ivanseidel/Primo/Photos-Bricks/Bricks.jpg

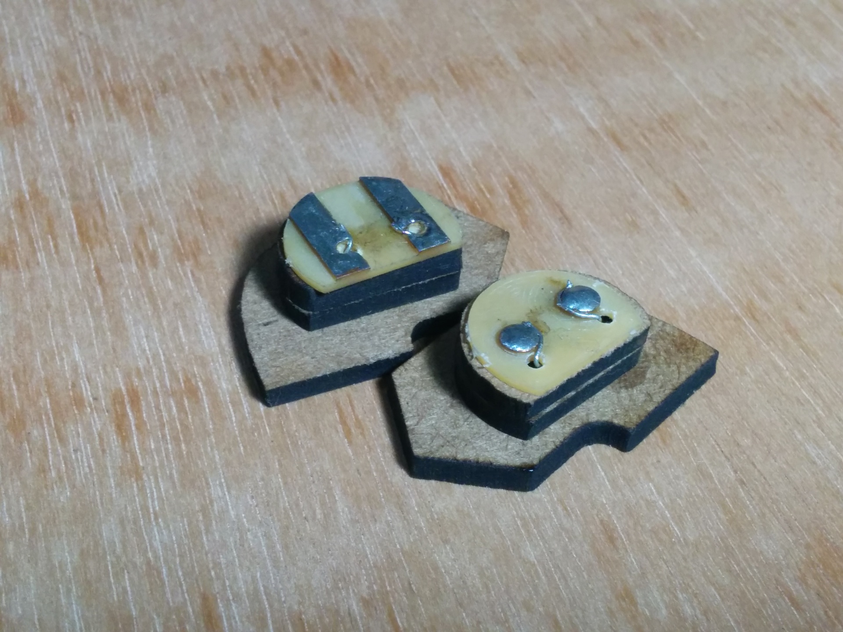
Photos-Bricks/Bricks.jpg
