ivanseidel/Primo/Photos-Cubetto/Cubetto_02.jpg

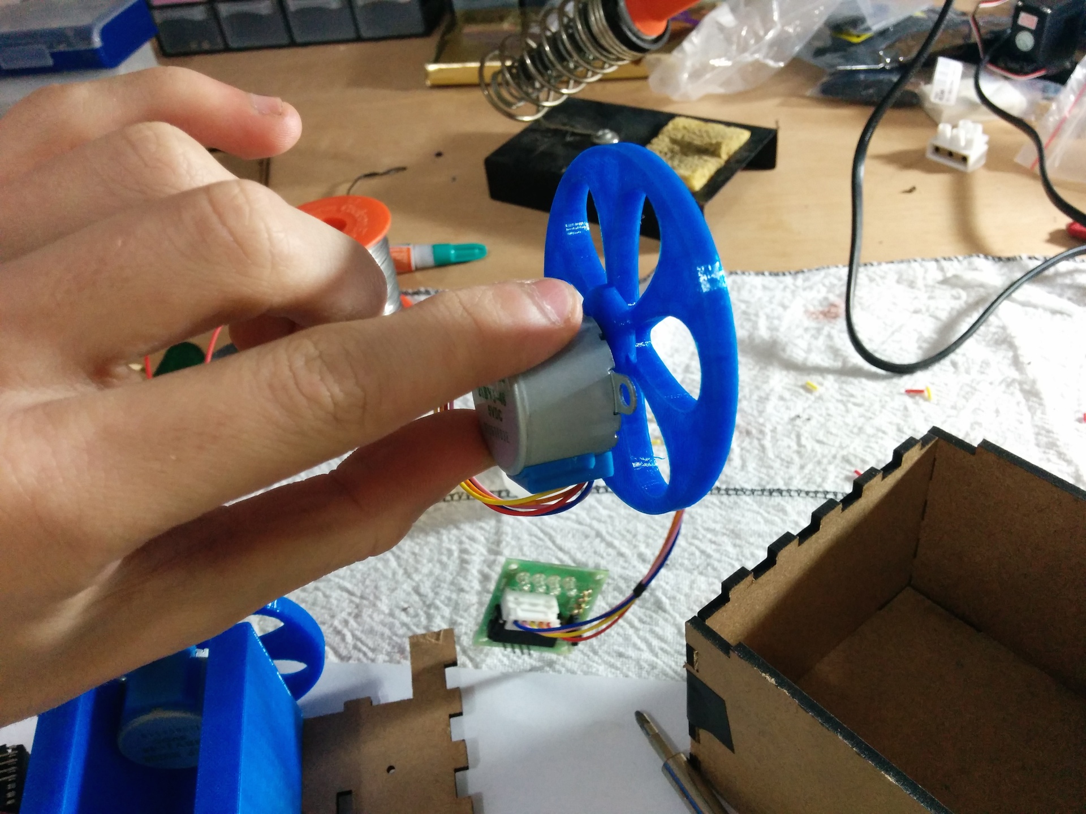
Photos-Cubetto/Cubetto_02.jpg
