ivanseidel/Primo/Photos-Cubetto/Cubetto_03.jpg

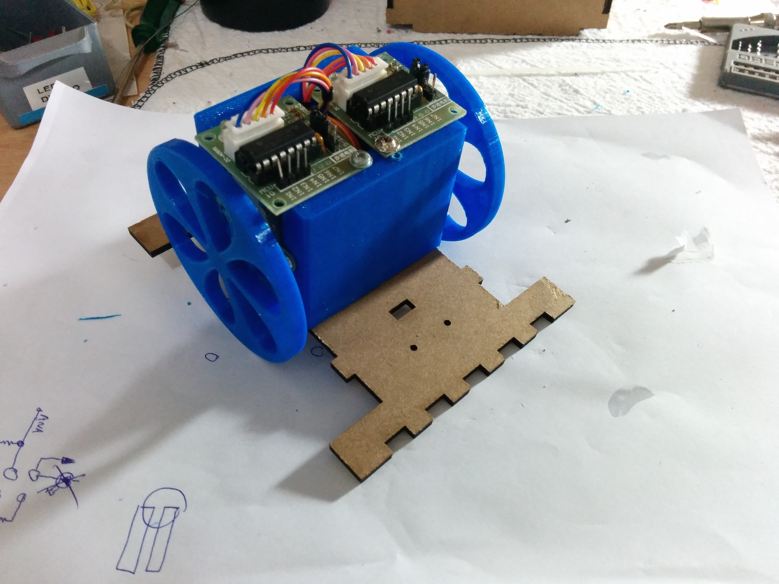
Photos-Cubetto/Cubetto_03.jpg
