ivanseidel/Primo/Photos-Cubetto/Cubetto_04.jpg

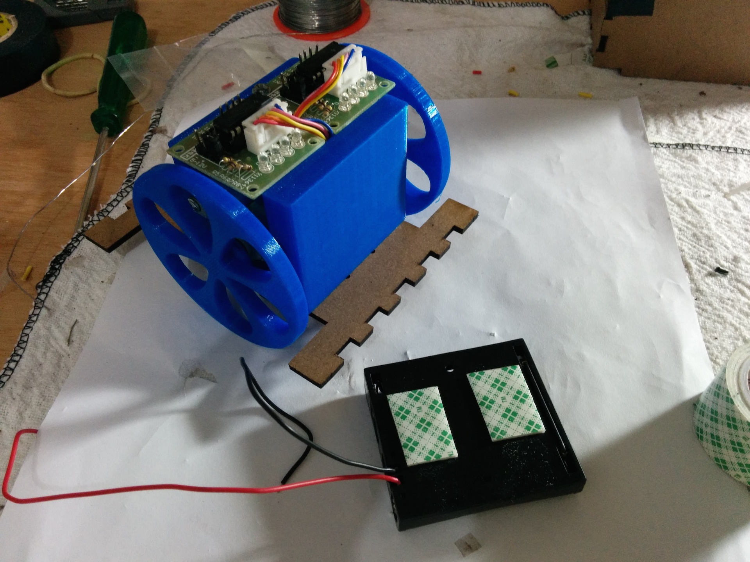
Photos-Cubetto/Cubetto_04.jpg
