ivanseidel/Primo/Photos-Cubetto/Cubetto_05.jpg

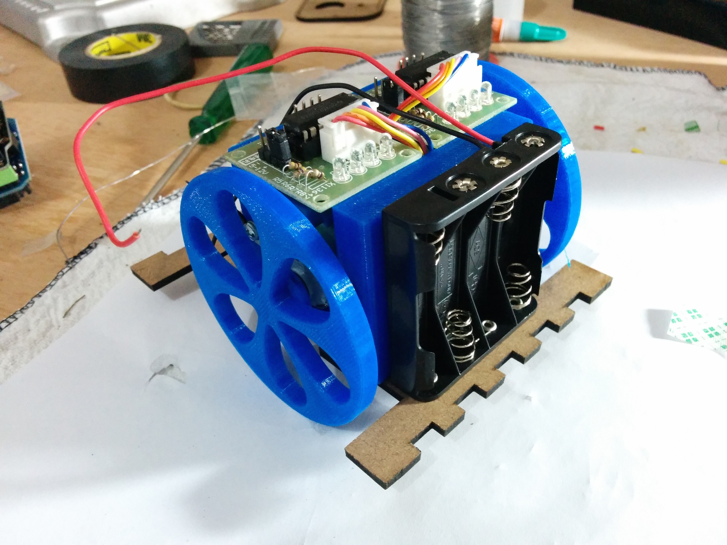
Photos-Cubetto/Cubetto_05.jpg
