ivanseidel/Primo/Photos-Cubetto/Cubetto_06.jpg

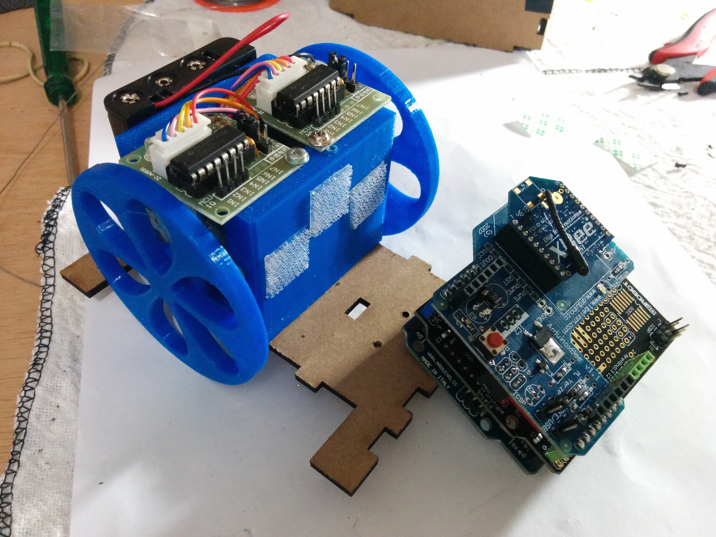
Photos-Cubetto/Cubetto_06.jpg
