ivanseidel/Primo/Photos-Cubetto/Cubetto_07.jpg

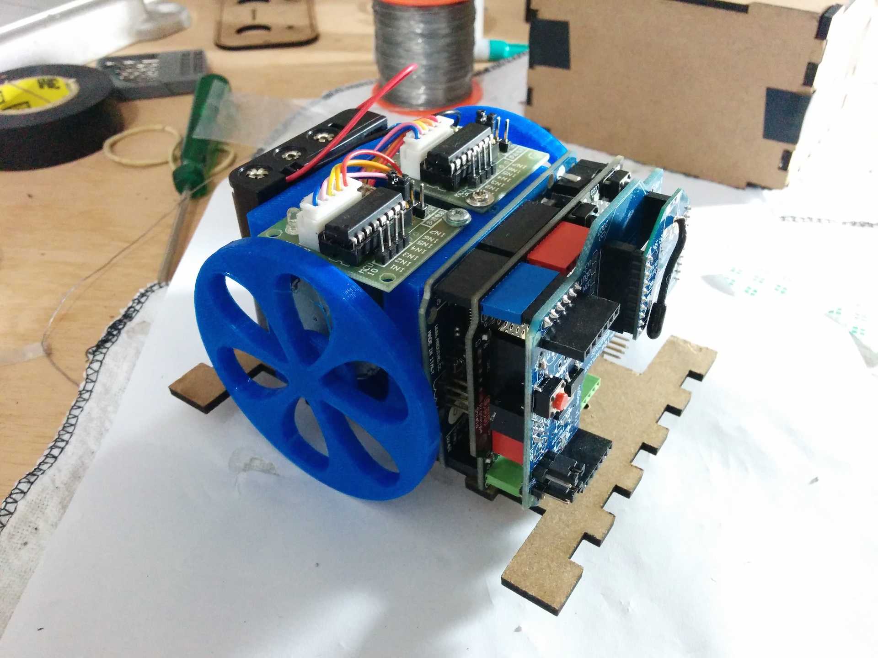
Photos-Cubetto/Cubetto_07.jpg
