ivanseidel/Primo/Photos-Cubetto/Cubetto_08.jpg

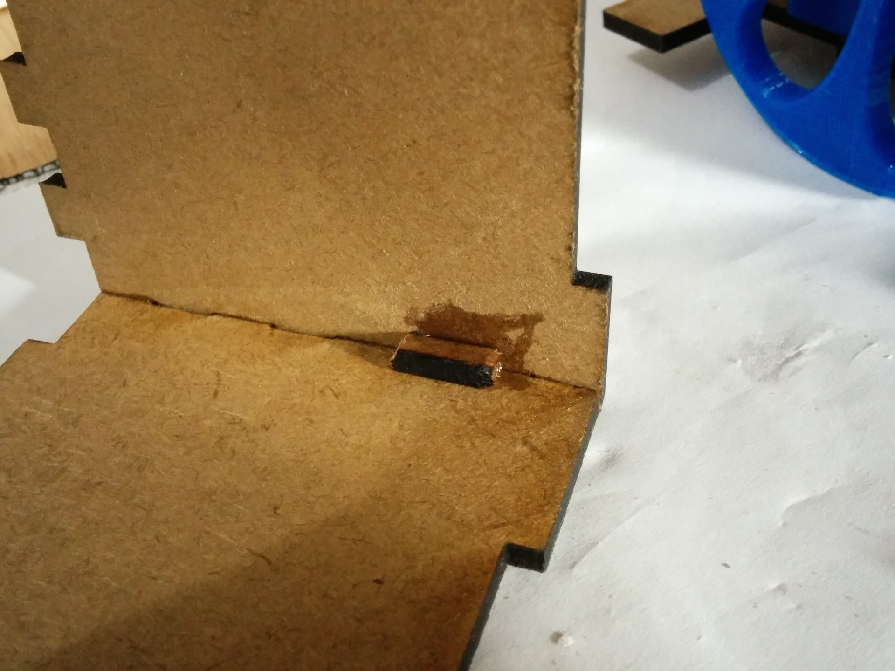
Photos-Cubetto/Cubetto_08.jpg
