ivanseidel/Primo/Photos-Cubetto/Cubetto_09.jpg

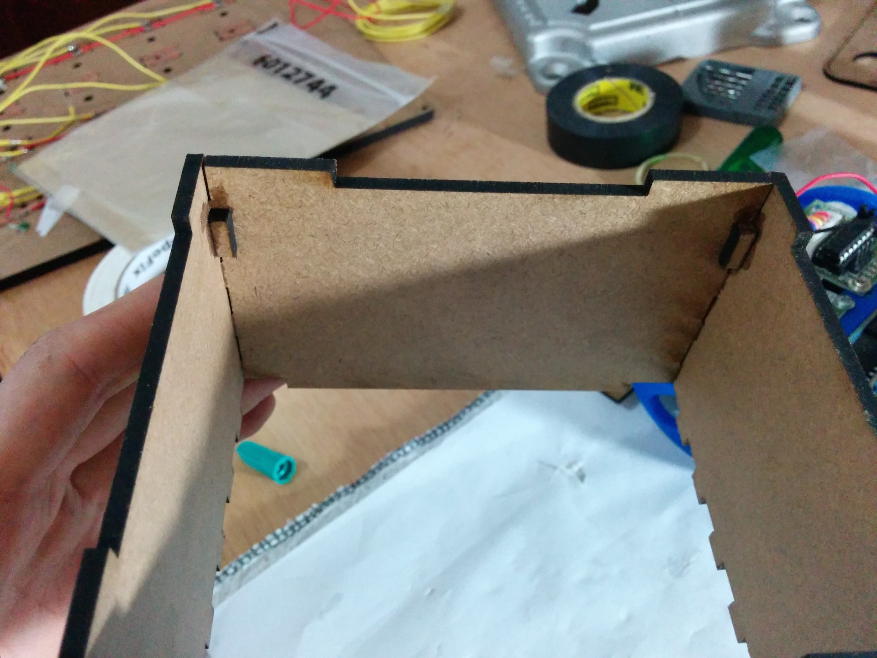
Photos-Cubetto/Cubetto_09.jpg
