ivanseidel/Primo/Photos-Cubetto/Cubetto_10.jpg

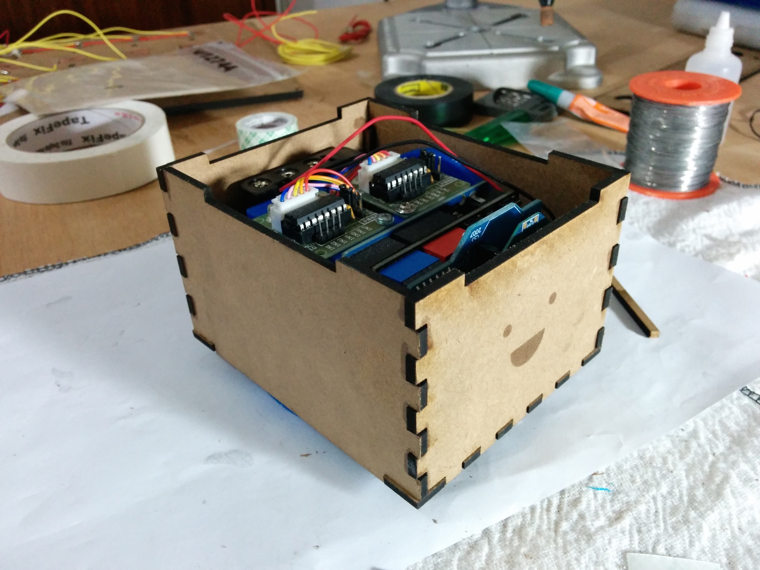
Photos-Cubetto/Cubetto_10.jpg
