ivanseidel/Primo/Photos-Cubetto/Cubetto_11.jpg

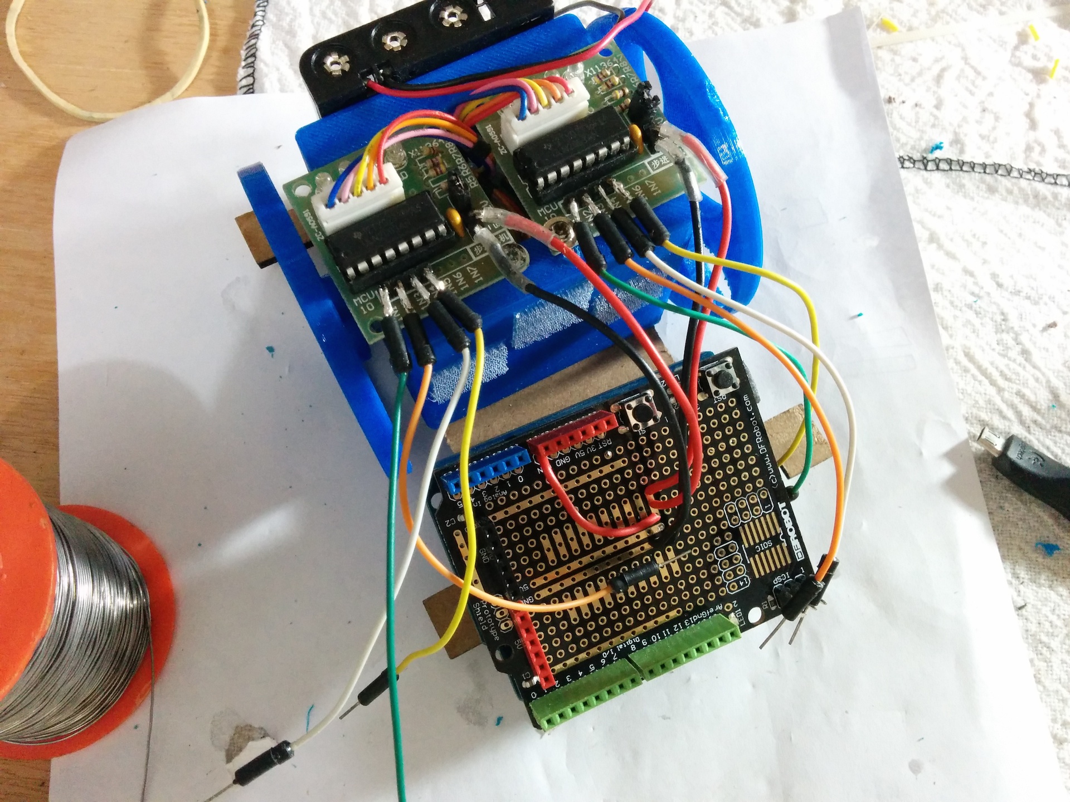
Photos-Cubetto/Cubetto_11.jpg
