ivanseidel/Primo/Photos-MainBoard/MainBoard_01.jpg

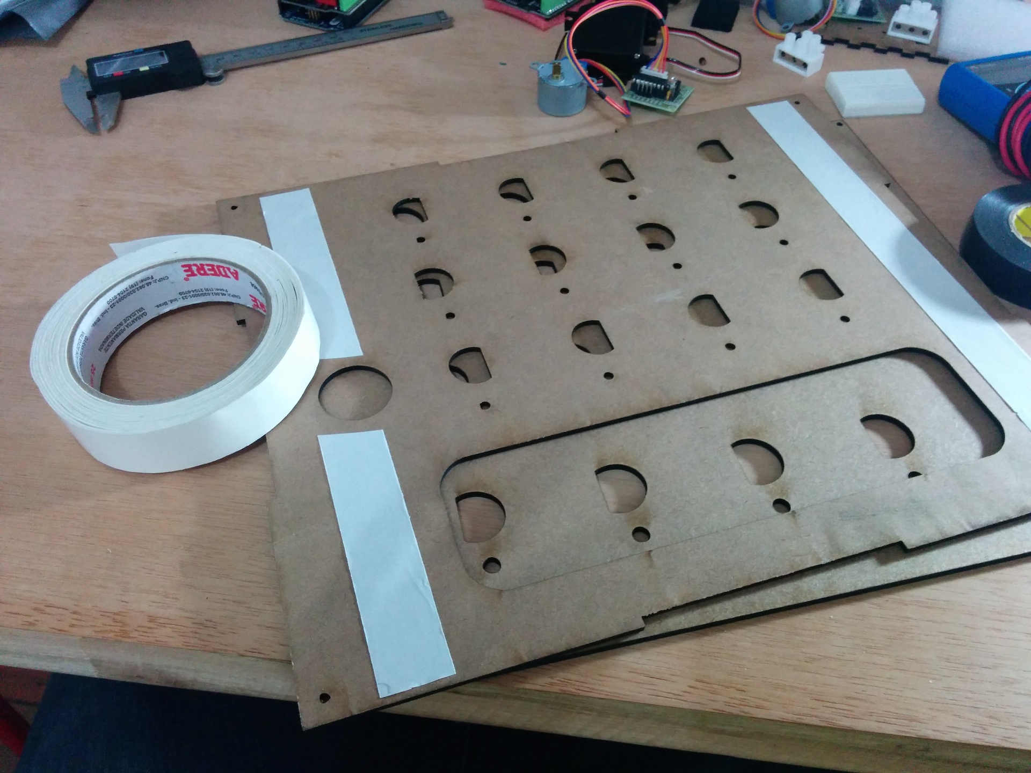
Photos-MainBoard/MainBoard_01.jpg
