ivanseidel/Primo/Photos-MainBoard/MainBoard_02.jpg

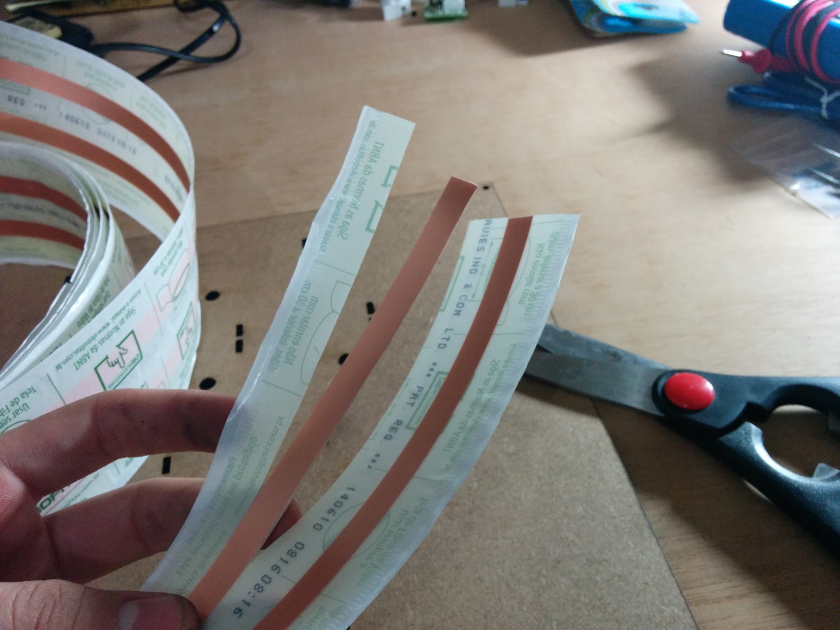
Photos-MainBoard/MainBoard_02.jpg
