ivanseidel/Primo/Photos-MainBoard/MainBoard_03.jpg

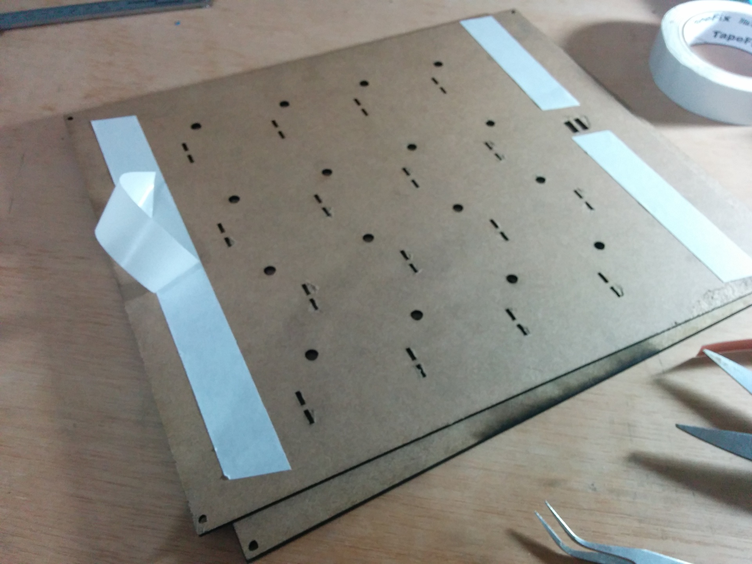
Photos-MainBoard/MainBoard_03.jpg
