ivanseidel/Primo/Photos-MainBoard/MainBoard_05.jpg

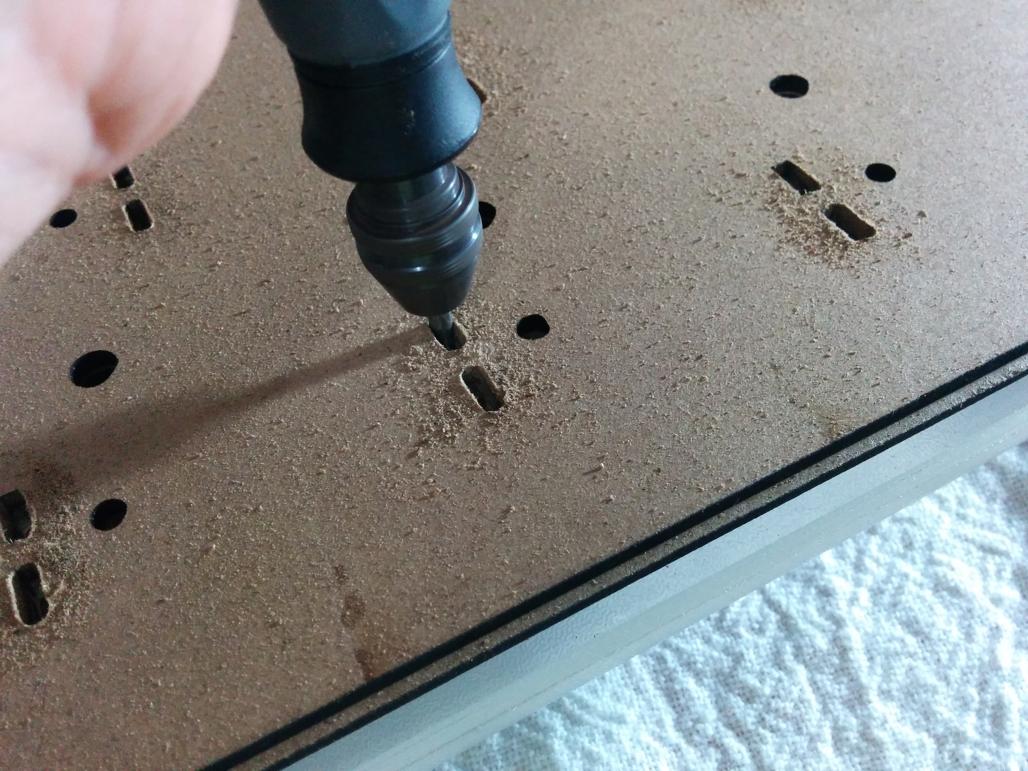
Photos-MainBoard/MainBoard_05.jpg
