ivanseidel/Primo/Photos-MainBoard/MainBoard_06.jpg

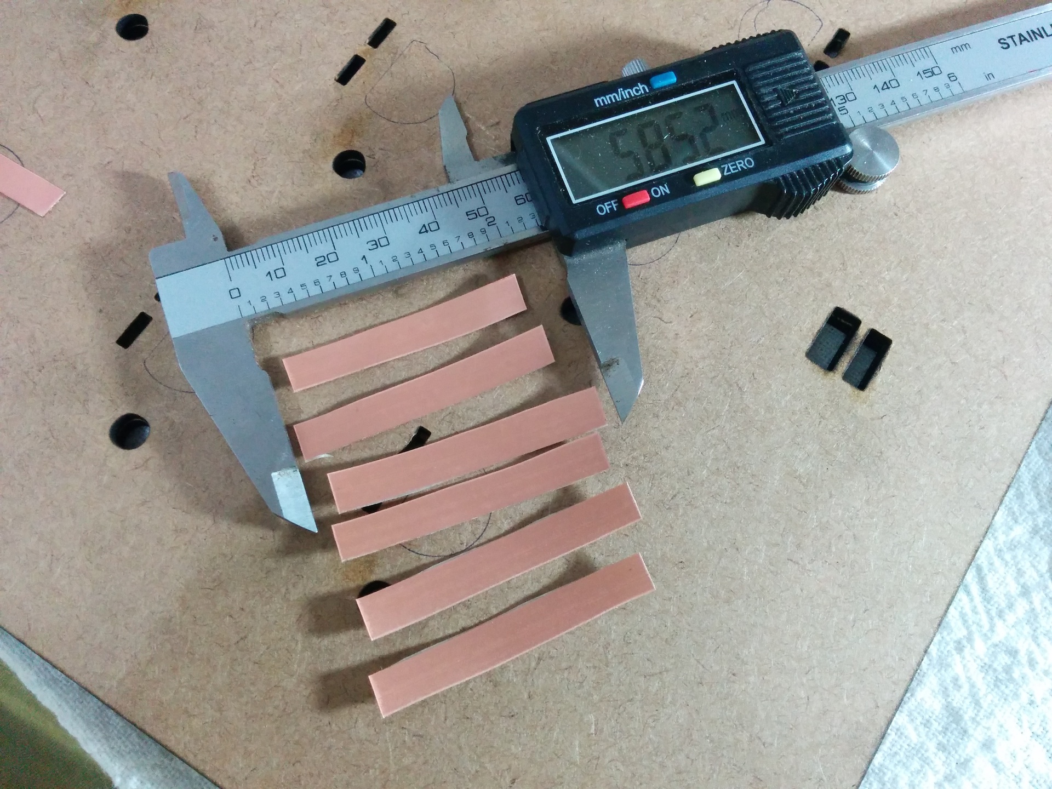
Photos-MainBoard/MainBoard_06.jpg
