ivanseidel/Primo/Photos-MainBoard/MainBoard_08.jpg

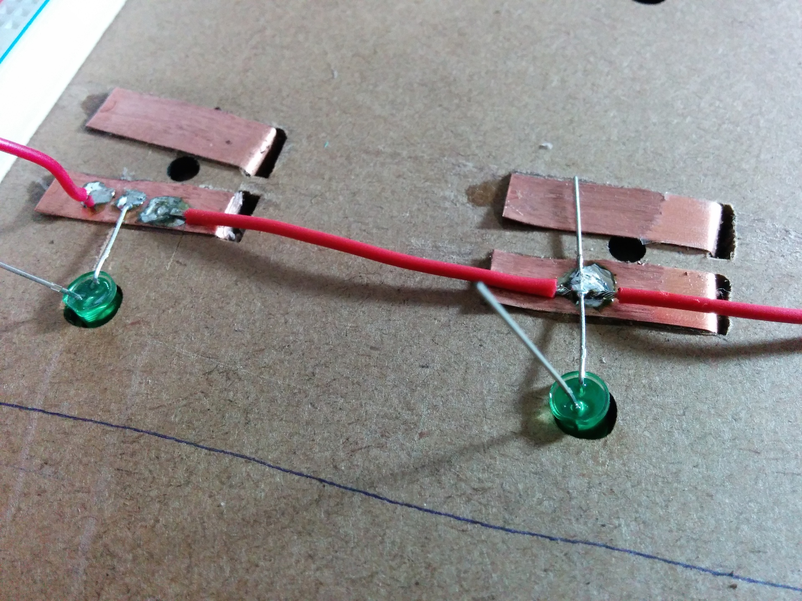
Photos-MainBoard/MainBoard_08.jpg
