ivanseidel/Primo/Photos-MainBoard/MainBoard_09.jpg

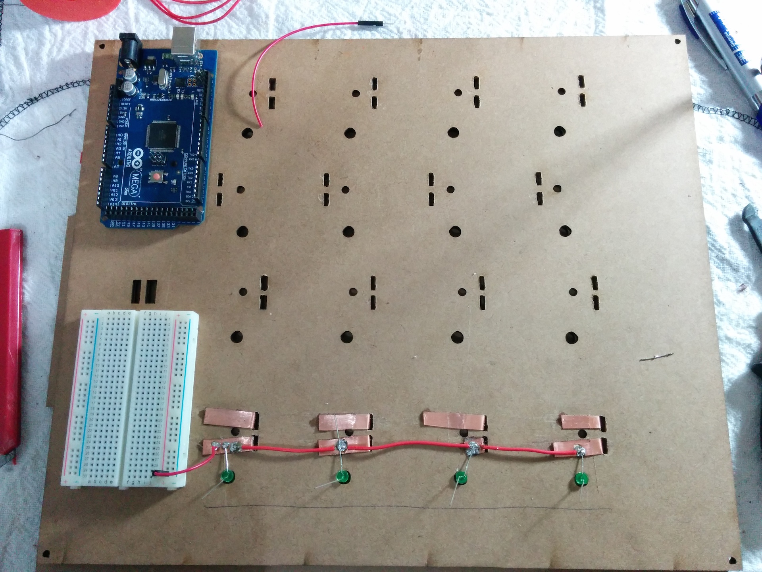
Photos-MainBoard/MainBoard_09.jpg
