ivanseidel/Primo/Photos-MainBoard/MainBoard_11.jpg

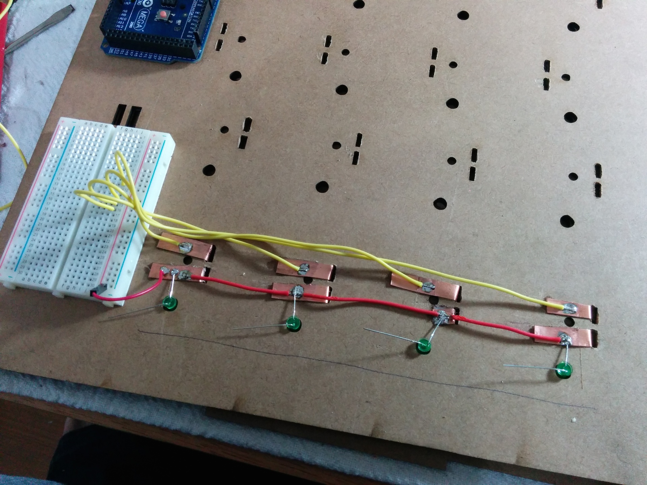
Photos-MainBoard/MainBoard_11.jpg
