ivanseidel/Primo/Photos-MainBoard/MainBoard_12.jpg

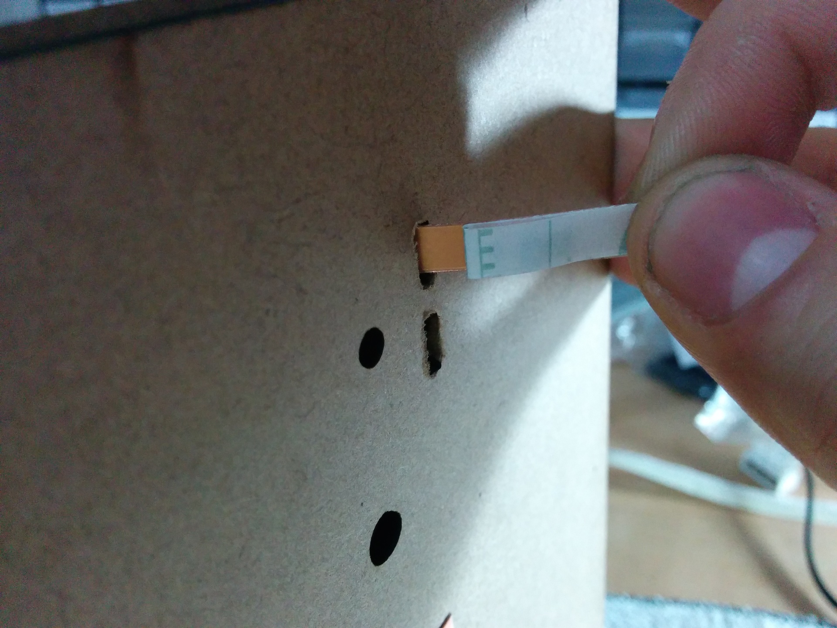
Photos-MainBoard/MainBoard_12.jpg
