ivanseidel/Primo/Photos-MainBoard/MainBoard_13.jpg

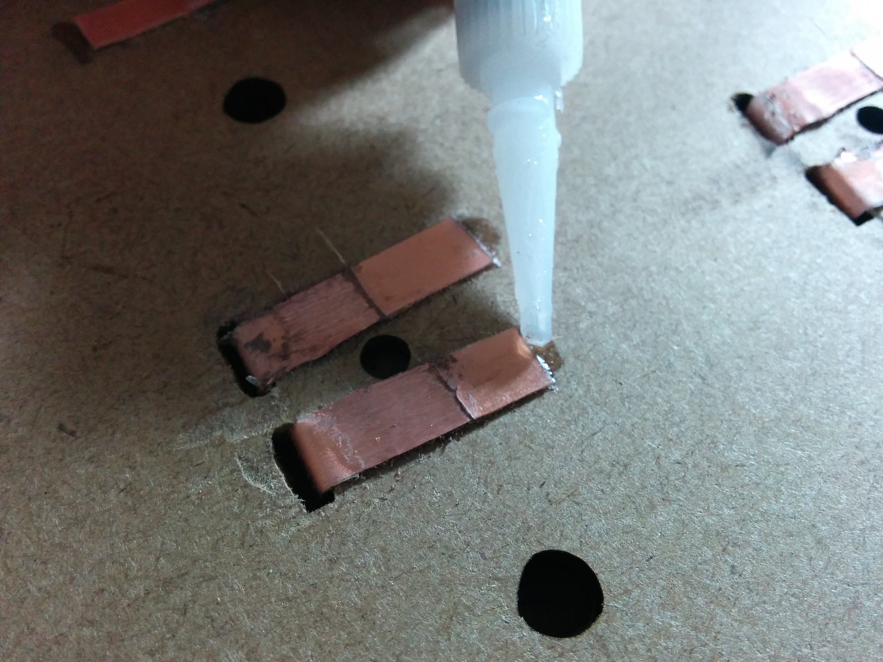
Photos-MainBoard/MainBoard_13.jpg
