ivanseidel/Primo/Photos-MainBoard/MainBoard_14.jpg

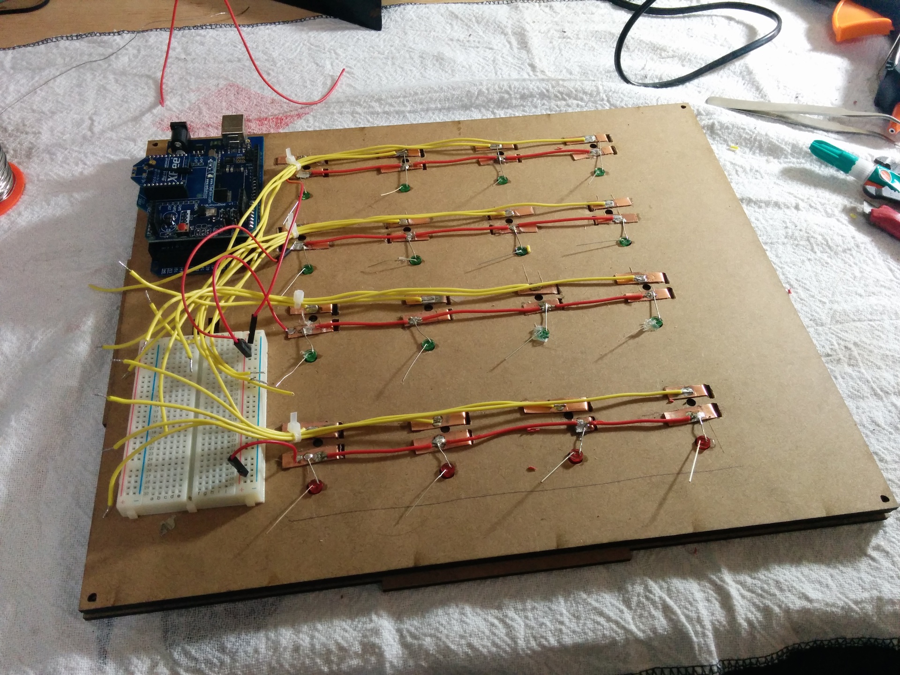
Photos-MainBoard/MainBoard_14.jpg
