ivanseidel/Primo/Photos-MainBoard/MainBoard_15.jpg

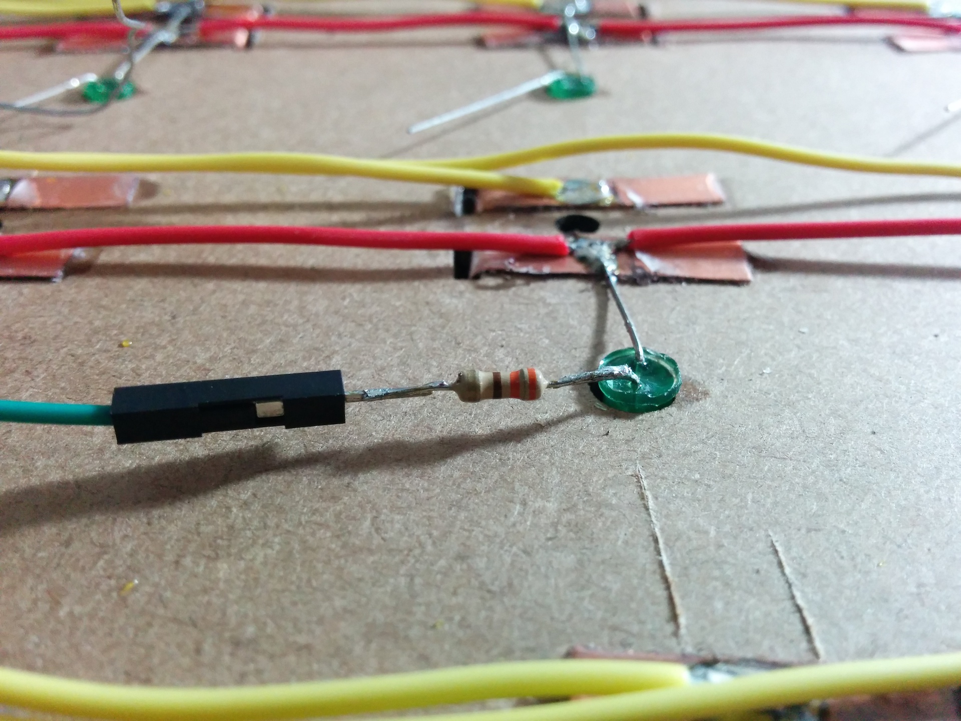
Photos-MainBoard/MainBoard_15.jpg
