ivanseidel/Primo/Photos-MainBoard/MainBoard_16.jpg

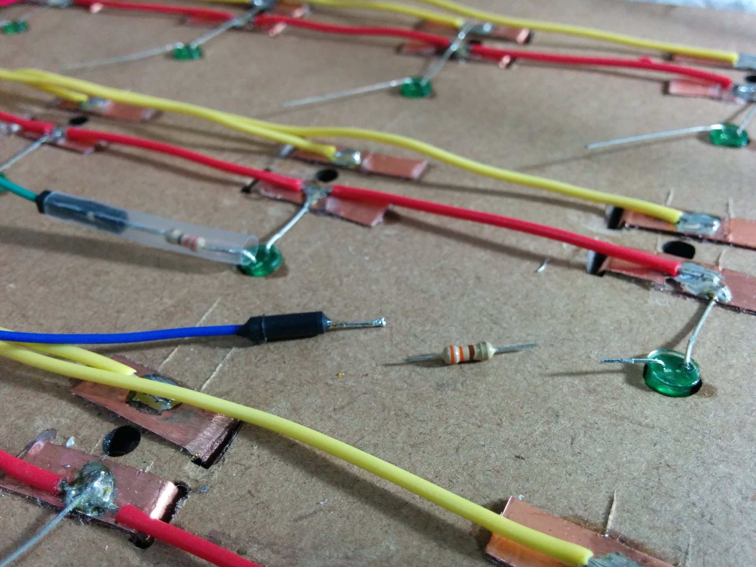
Photos-MainBoard/MainBoard_16.jpg
