ivanseidel/Primo/Photos-MainBoard/MainBoard_17.jpg

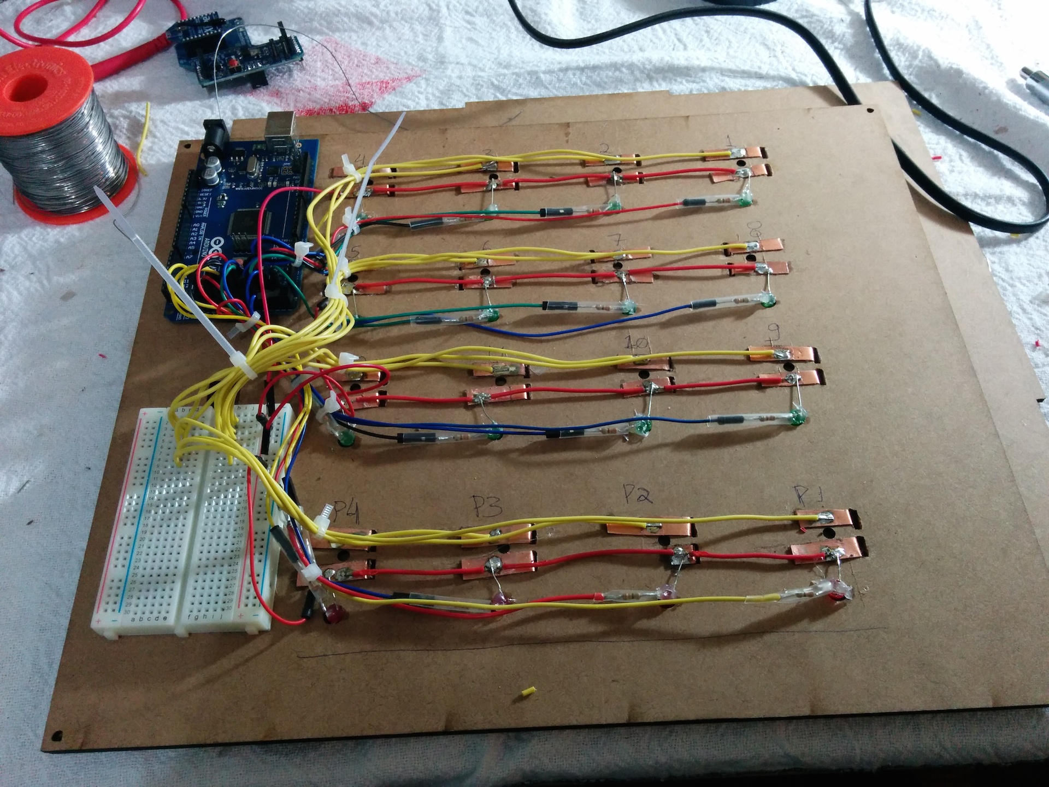
Photos-MainBoard/MainBoard_17.jpg
