ivanseidel/Primo/Photos-MainBoard/MainBoard_18.jpg

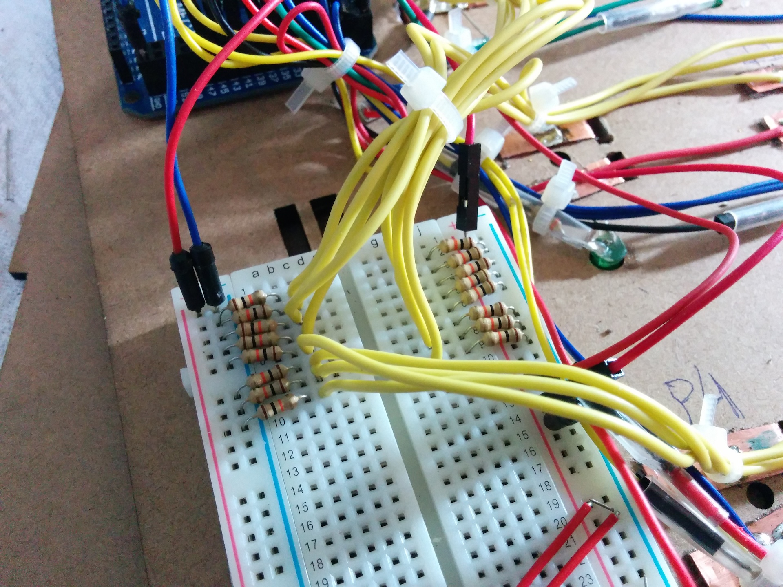
Photos-MainBoard/MainBoard_18.jpg
