ivanseidel/Primo/Photos-MainBoard/MainBoard_19.jpg

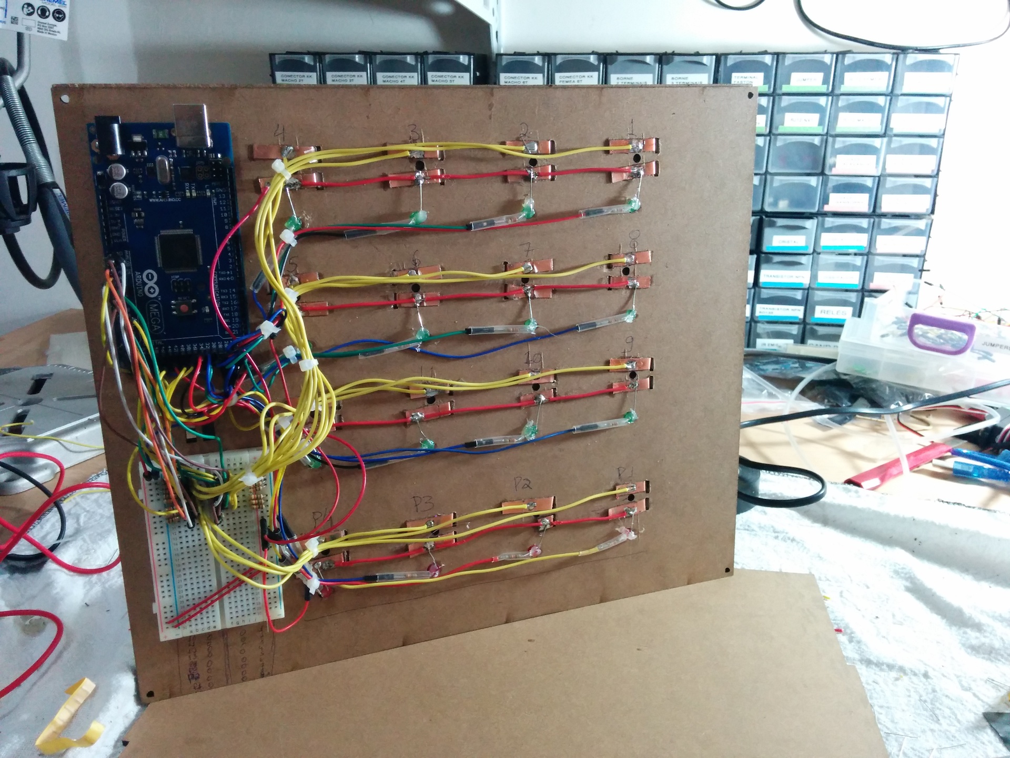
Photos-MainBoard/MainBoard_19.jpg
