ivanseidel/Primo/Photos-MainBoard/MainBoard_20.jpg

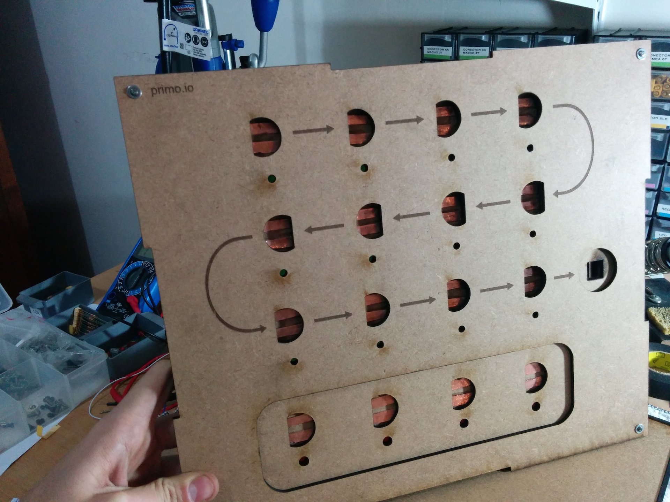
Photos-MainBoard/MainBoard_20.jpg
