ivanseidel/Primo/Photos-MainBoard/MainBoard_21.jpg

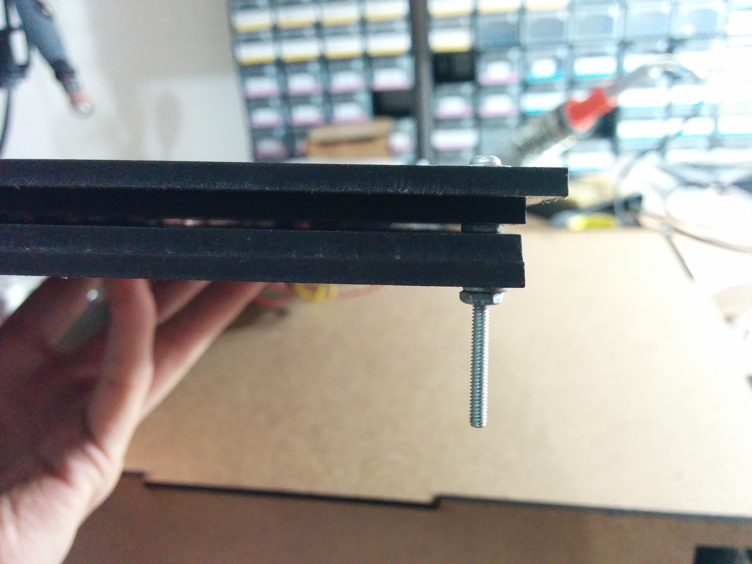
Photos-MainBoard/MainBoard_21.jpg
