ivanseidel/Primo/Photos-MainBoard/MainBoard_22.jpg

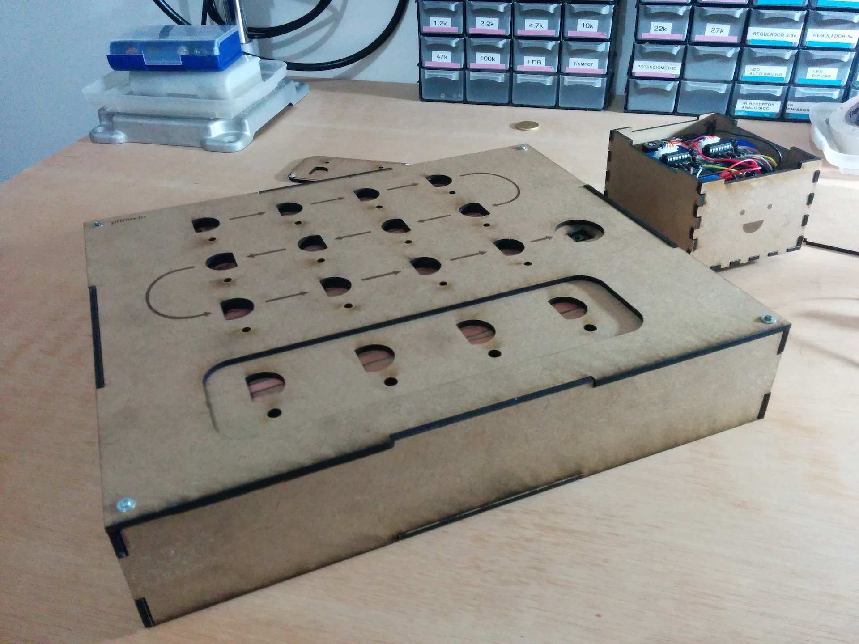
Photos-MainBoard/MainBoard_22.jpg
