ivanseidel/Primo/Photos-MainBoard/MainBoard_23.jpg

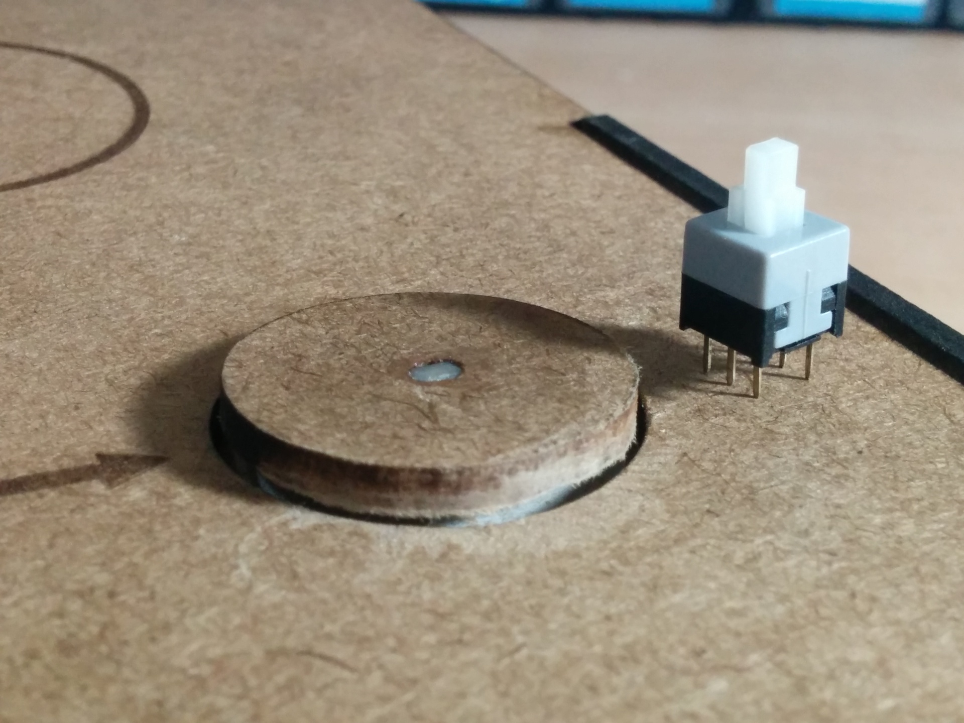
Photos-MainBoard/MainBoard_23.jpg
