ivanseidel/Primo/Photos-MainBoard/MainBoard_24.jpg

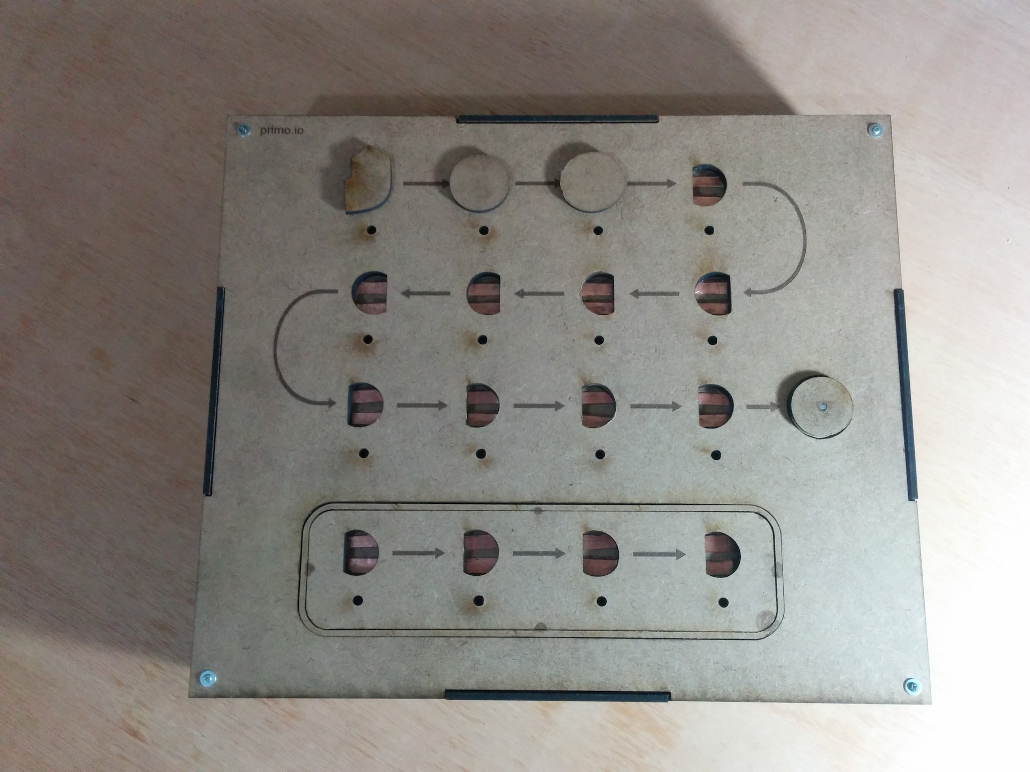
Photos-MainBoard/MainBoard_24.jpg
