ivanseidel/Primo/Photos-MainBoard/MainBoard_25.jpg

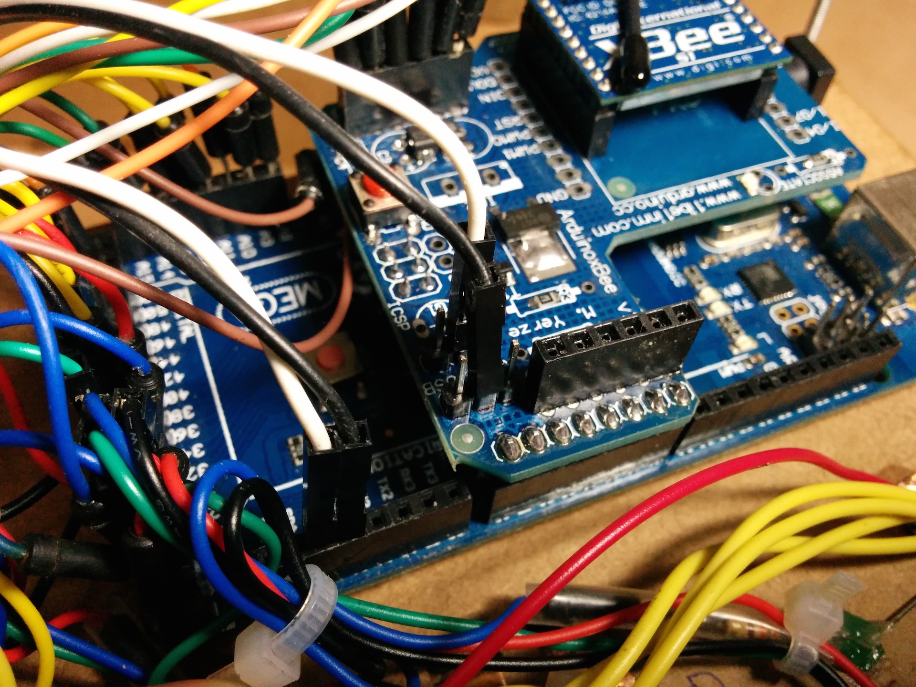
Photos-MainBoard/MainBoard_25.jpg
